Jegeva/BruCON_2021/firmware/main/menu.c

#include "menu.h"
#include "nokialcd.h"
#include "expat.h"
#include "wifi.h"
#if defined(CONFIG_HARDWARE_2020) || defined(CONFIG_HARDWARE_2019)
#include "touch.h"
#include "math.h"
#include "leds.h"
#include <soc/soc.h>
#include <esp_system.h>
#include "battery.h"
#include "sensor.h"
#include "brucon_nvs.h"
#include "mqtt.h"
#endif

uint8_t    menu_dirty    = 1;
uint8_t    currselected  = 0;
menuItem * currMenuItem = NULL ;
char     * statusbartext =NULL;
int        statusbartextallocedssz = 0;

menuItp menuhead;
menuItp schedhead_d1;
menuItp schedhead_d2;
menuItp schedhead_d3;





menuItem fakeplaceholder;
volatile char notaskbar = 0;

void display_skeleton();
void display_taskbar();

void setnotaskbar(int i){
  notaskbar=i;
}

void fixparent(menuItp p, menuItp h)
{
    while(h != NULL){
        h->parent = p;
        h=h->next;
    }
}

char skeleton_inited = 0;

void sched03(void* arg){
    currMenuItem->child = schedhead_d1;
    fixparent(currMenuItem,currMenuItem->child);
    currMenuItem->funcp = NULL;
    manage_click_menu(PIN_BR,0);
};

void sched04(void* arg){
    currMenuItem->child = schedhead_d2;
    fixparent(currMenuItem,currMenuItem->child);
    currMenuItem->funcp = NULL;
    manage_click_menu(PIN_BR,0);

};

void sched05(void* arg){
    currMenuItem->child = schedhead_d3;
    fixparent(currMenuItem,currMenuItem->child);
    currMenuItem->funcp = NULL;
    manage_click_menu(PIN_BR,0);
};



void MapWest(void* arg){
    fakeplaceholder.parent = currMenuItem;
    currMenuItem = &fakeplaceholder;
    MapWestL(arg);
    lcd_sync();
    skeleton_inited = 0;
}

void MapNovo(void* arg){
    fakeplaceholder.parent = currMenuItem;
    currMenuItem = &fakeplaceholder;
    MapNovoL(arg);
    lcd_sync();
    skeleton_inited = 0;
}

void VivaLaVodka(void * arg)
{
  notaskbar=1;
  // for you richard...
  fakeplaceholder.parent = currMenuItem;
  currMenuItem = &fakeplaceholder;
  /*uint32_t score = */
  VivaLaVodkaL(NULL);
  skeleton_inited = 0;
 
}
void VivaLaToothpaste(void * arg)
{
  notaskbar=1;
  // for you richard...
  fakeplaceholder.parent = currMenuItem;
  currMenuItem = &fakeplaceholder;
  /*uint32_t score = */
  VivaLaVodkaL((void*)1);
  skeleton_inited = 0;

}
uint32_t VivaLaToothpasteDirect(void * arg)
{
  // for you richard...
  fakeplaceholder.parent = currMenuItem;
  currMenuItem = &fakeplaceholder;
  /*uint32_t score = */
  uint32_t r=VivaLaVodkaL((void*)1);
  skeleton_inited = 0;
  return r;
}
void SystemInfoL(void* arg)
{
    char * wrkstr = calloc(128,sizeof(char));
    esp_chip_info_t chip_info;
    uint8_t mac[6] ;
    esp_efuse_mac_get_default(mac);
    esp_chip_info(&chip_info);
    memset(wrkstr,0,128);
    lcd_clearB12(B12_WHITE);
    sprintf(wrkstr,"mac %x:%x:%x:%x:%x:%x",
            mac[0],mac[1],mac[2],mac[3],mac[4],mac[5]);

    lcd_setStr(wrkstr,16,2,B12_BLACK,B12_WHITE,0,0);
    sprintf(wrkstr,"%d cores, WiFi%s%s",
            chip_info.cores,
            (chip_info.features & CHIP_FEATURE_BT) ? "/BT" : "",
            (chip_info.features & CHIP_FEATURE_BLE) ? "/BLE" : "");
    lcd_setStr(wrkstr,26,2,B12_BLACK,B12_WHITE,0,0);
    sprintf(wrkstr,"Freq:%dMHz", APB_CLK_FREQ/(1000*1000));
    lcd_setStr(wrkstr,36,2,B12_BLACK,B12_WHITE,0,0);
    sprintf(wrkstr,"bat %d mV %d%%", batteryinfo.vbat,batteryinfo.percent);
    lcd_setStr(wrkstr,46,2,B12_BLACK,B12_WHITE,0,0);
    sprintf(wrkstr,"WiFi ssid: %s", WIFI_SSID);
    lcd_setStr(wrkstr,56,2,B12_BLACK,B12_WHITE,0,0);
    sprintf(wrkstr,"WiFi pw: %s", WIFI_PASSWORD);
    lcd_setStr(wrkstr,66,2,B12_BLACK,B12_WHITE,0,0);

    free(wrkstr);
    display_taskbar();

}



void SystemInfo(void* arg)
{
    fakeplaceholder.parent = currMenuItem;
    currMenuItem = &fakeplaceholder;
    SystemInfoL(NULL);
    lcd_sync();
    skeleton_inited = 0;
}

void EraseKeys(void* arg){
  if( getBruCONConfigFlag("haveKeys") ){
    printf("Erasing keys!\n");
    BruCONErase_key("haveKeys");
    BruCONErase_key("haveClientCert");
    BruCONErase_key("ClientCert");
    BruCONErase_key("POWER_HISTORY");
    BruCONErase_key("UNIQUE_ID");
    BruCONErase_key("EVERSION");
    BruCONErase_key("haveAlcCal");
    printf("Erased keys!\n");
  }
  
}

void RebootF(void* arg){
  printf("REBOOT!\n");
  esp_restart();
}

void testMQTT(void* arg)
{
  printf("TEST MQTT !\n");
  MQTT_Start();
}

void testF(void* arg)
{
  printf("TEST !\n");
  nextwheel(25); 
}
void testF1(void* arg)
{
  printf("TEST 1!\n");
  nextwheelpow(25);
}
void testF2(void* arg)
{
  printf("TEST 2!\n");
  //taskColorWheel();
  taskColorAdvertise();
}

void dispSchedItem(void* arg){
    lcd_clearB12(B12_WHITE);
    char * wrkstr = calloc(128,sizeof(char));
    notaskbar=1;

    memset(wrkstr,0,128);
    sprintf(wrkstr,"Loc: %s",currMenuItem->schedloc);
    lcd_setStr(wrkstr,2,0,B12_BLACK,B12_WHITE,0,1);

    switch(currMenuItem->schedtype){
    case 'W':
        sprintf(wrkstr,"Type: Workshop");
        break;
    case 'T':
        sprintf(wrkstr,"Type: Talk");
        break;

    case 'L':
        sprintf(wrkstr,"Type: General");
        break;

    case 'V':
        sprintf(wrkstr,"Type: Village");

        break;

    case 'S':
        sprintf(wrkstr,"Type: Sp3ci4l");
        break;
    default:
        printf("unknown type %c\n",currMenuItem->schedtype);
    }

    lcd_setStr(wrkstr,32,0,B12_BLACK,B12_WHITE,0,1);
    lcd_setRect(30,0, 30,131, 1, 0);
    lcd_setRect(47,0, 94,131, 1, B12_RED);
    lcd_setStr(currMenuItem->menuText+12,48,0,B12_WHITE,B12_RED,0,1);
    lcd_setRect(46,0, 46,131, 1, 0);
    if(currMenuItem->schedspk != NULL)
        lcd_setStr(currMenuItem->schedspk,96,0,B12_BLACK,B12_WHITE,0,1);
    lcd_setRect(94,0, 94,131, 1, 0);
    free(wrkstr);
    fakeplaceholder.parent = currMenuItem;
    currMenuItem = &fakeplaceholder;

    lcd_sync();
}


#define AUTHORIZED_FUNC_NBR 12

void * menuAuthorisedFunc[AUTHORIZED_FUNC_NBR] = {
    sched03,
    sched04,
    MapWest,
    MapNovo,
    SystemInfo,
    testF,
    testF1,
    testF2,
    RebootF,
    EraseKeys,
    VivaLaVodka,
    VivaLaToothpaste
};

const char * menuAuthorisedFuncName[AUTHORIZED_FUNC_NBR] = {
    "sched03",
    "sched04",
    "MapWest",
    "MapNovo",
    "SystemInfo",
    "testF",
    "testF1",
    "testF2",
    "Reboot",
    "EraseKeys",
    "VivaLaVodka",
    "VivaLaToothpaste"
};

void (*volatile menu_mgt_func)(uint32_t,uint32_t);

void manage_click_menu(uint32_t value,uint32_t level ){
  printf("manage click %d %d\n",value, level);
  menu_mgt_func(value,level);
}

void manage_click_menu_orig(uint32_t value,uint32_t level ){

    int oldrank=currselected;
    menuItem * oldmenuitem = currMenuItem;

//r    printf("click : %d\n",value);

    if(currMenuItem == NULL){
        printf("CURR NULL!\n");

        return;

    }
    //  if(value == PIN_NCHARGING){
    //     printf("clkc: ncharg %d \n",level);
    // }
    if(value == 9999)
        level = 0;

    if(level==0){
//        printf("clkc: %d \n",value);
        if(value != PIN_NCHARGING  && value != 9999){

            switchbacklight(1);
            last_click=xTaskGetTickCount();
            start_bat_task();


        }

        switch(value){
        case 9999:
            display_taskbar();

            printf("battery update : %d vbat : %d mV %d%%\n",  batteryinfo.powstat,batteryinfo.vbat,batteryinfo.percent);
            batt_update=0;
            lcd_sync();
            return;
        case PIN_BL:
            if(currMenuItem->parent != NULL){
                notaskbar=0;
                currMenuItem = currMenuItem->parent;
                currselected = currMenuItem->rank;
                menu_dirty    = 1;
            }
            break;
        case PIN_BR:
            if(currMenuItem->funcp != NULL){
                menu_dirty    = 0;
                currMenuItem->funcp(NULL);
            } else {
               if(currMenuItem->child != NULL){
                    currMenuItem = currMenuItem->child;
                    currselected = currMenuItem->rank;
                    menu_dirty    = 1;
                }
            }
            break;
        case PIN_BU:
            if(currMenuItem->prev != NULL){
                currMenuItem = currMenuItem->prev;
                currselected = currMenuItem->rank;
                menu_dirty    = 1;
            }
            break;
        case PIN_BD:
            if(currMenuItem->next != NULL){
                currMenuItem = currMenuItem->next;
                currselected = currMenuItem->rank;
                menu_dirty    = 1;
            }
            break;
        case PIN_BA:
            if(currMenuItem->parent != NULL){
                notaskbar=0;
                currMenuItem = currMenuItem->parent;
                currselected = currMenuItem->rank;
                menu_dirty    = 1;
            }
            break;
        case PIN_BB:

            if(currMenuItem->funcp != NULL){
                menu_dirty    = 0;
                currMenuItem->funcp(NULL);
            } else {

                if(currMenuItem->child != NULL){
                    currMenuItem = currMenuItem->child;
                    currselected = currMenuItem->rank;
                    menu_dirty    = 1;
                }
            }
            break;
        }
    }
    if(menu_dirty){

        if( ( (value ==PIN_BU ) || ( value == PIN_BD)           ) ){

        if((currselected != 0) && (((currselected%7)==0)&& (value == PIN_BD) ) ){
            return;
        }

        if((value ==PIN_BU ) && (oldrank == 7) )
            return;


        lcd_setRect((((oldrank%7)+1)*16)+1,0, (((oldrank%7)+2)*16)-1,131, 1, B12_WHITE);
        lcd_setStr(oldmenuitem->menuText,(((oldrank%7)+1)*16)+2,0,B12_BLACK,B12_WHITE,0,0);
        lcd_setRect((((currselected%7)+1)*16)+1,0, (((currselected%7)+2)*16)-1,131, 1, B12_RED);
        lcd_setStr(currMenuItem->menuText,(((currselected%7)+1)*16)+2,0,B12_WHITE,B12_RED,0,0);
        lcd_setRect(((oldrank%7)+1)*16,0, ((oldrank%7)+1)*16,131, 1, 0);
        lcd_setRect(((currselected%7)+1)*16,0,((currselected%7)+1)*16,131, 1, 0);
        menu_dirty=1;
        lcd_sync();
        } else {
            ;

        }
    }

}
void * menuAuthorisedFuncByName(char * funcname){
    int i;
    for(i=0;i<AUTHORIZED_FUNC_NBR;i++){
        if(strcmp(funcname,menuAuthorisedFuncName[i]) == 0){
            return menuAuthorisedFunc[i];
        }
    }
    return NULL;
}

void parserMenuTree(menuItp acurrmenuItem,const cJSON* subtree, int depth){
    cJSON *elptr = NULL;
    const cJSON *thisel = NULL;
    menuItp currmenuItem=acurrmenuItem;
    cJSON_ArrayForEach(elptr, subtree){

        thisel = cJSON_GetObjectItemCaseSensitive(elptr, "menutitle");
        if (cJSON_IsString(thisel) && (thisel->valuestring != NULL))
            currmenuItem->menuText= thisel->valuestring;

        thisel = cJSON_GetObjectItemCaseSensitive(elptr, "rank");
        if (cJSON_IsNumber(thisel))
            currmenuItem->rank    = thisel->valueint;

        thisel = cJSON_GetObjectItemCaseSensitive(elptr, "function");
        if (cJSON_IsString(thisel) && (thisel->valuestring != NULL)){
            currmenuItem->funcp = menuAuthorisedFuncByName(thisel->valuestring);
            if(currmenuItem->funcp == NULL){
                printf("unauthorised json function: %s\n",thisel->valuestring);
            }
        }
        thisel = cJSON_GetObjectItemCaseSensitive(elptr, "submenus");
        if(cJSON_IsArray(thisel)){
            //      printf("\nrec\n");
            currmenuItem->child = (menuItp)calloc(1,sizeof(menuItem));
            currmenuItem->child->parent = currmenuItem;
            parserMenuTree(currmenuItem->child,thisel , depth+1);
        }
        if(elptr->next != NULL){
            currmenuItem->next = (menuItp)calloc(1,sizeof(menuItem));
            currmenuItem->next->prev = currmenuItem;
            currmenuItem->next->parent = acurrmenuItem->parent;
            currmenuItem = currmenuItem->next;
        }


    }
//    printf("\nD;%d\n",depth);

}




void parserSchedTreeT(menuItp acurrmenuItem,const cJSON* subtree, int depth){
    cJSON *elptr = NULL;
    const cJSON *thisel = NULL;
    int rank = 0;

    menuItp currmenuItem=acurrmenuItem;

    cJSON_ArrayForEach(elptr, subtree){
        thisel = cJSON_GetObjectItemCaseSensitive(elptr, "title");
        if (cJSON_IsString(thisel) && (thisel->valuestring != NULL)){
            currmenuItem->menuText= thisel->valuestring;
        }
        thisel = cJSON_GetObjectItemCaseSensitive(elptr, "evt");
        if (cJSON_IsString(thisel) && (thisel->valuestring != NULL)){
            currmenuItem->schedtype= *thisel->valuestring;
        }
        thisel = cJSON_GetObjectItemCaseSensitive(elptr, "loc");
        if (cJSON_IsString(thisel) && (thisel->valuestring != NULL)){
            currmenuItem->schedloc = thisel->valuestring;
        }
        thisel = cJSON_GetObjectItemCaseSensitive(elptr, "descr");
        if (cJSON_IsString(thisel) && (thisel->valuestring != NULL)){
            currmenuItem->schedentry = thisel->valuestring;
        }
        thisel = cJSON_GetObjectItemCaseSensitive(elptr, "spk");
        if (cJSON_IsString(thisel) && (thisel->valuestring != NULL)){
            currmenuItem->schedspk = thisel->valuestring;
        }
        currmenuItem->rank = rank++;
        currmenuItem->funcp = dispSchedItem;
        if(elptr->next != NULL){
            currmenuItem->next = (menuItp)calloc(1,sizeof(menuItem));
            currmenuItem->next->prev = currmenuItem;
            currmenuItem = currmenuItem->next;
        }

    }

}

void parserSchedTree(const cJSON* tree){
    schedhead_d1 = calloc(1,sizeof(struct menuIt));
    schedhead_d2 = calloc(1,sizeof(struct menuIt));
    //  schedhead_d3 = calloc(1,sizeof(struct menuIt));

    parserSchedTreeT(schedhead_d1,tree->child,0);
    parserSchedTreeT(schedhead_d2,tree->child->next,0);
    //parserSchedTreeT(schedhead_d3,tree->child->next->next,0);

}
void parserMenuJson(const char* jsonstring,uint8_t issched){
    cJSON *menu_json = cJSON_Parse(jsonstring);
    int depth = 0;
    if (menu_json == NULL)
    {
        const char *error_ptr = cJSON_GetErrorPtr();
        if (error_ptr != NULL){
            fprintf(stderr, "Error before: %s\n", error_ptr);
        }
    }
    if(issched){
        parserSchedTree(menu_json);
    } else {
        menuhead = (menuItp)calloc(1,sizeof(menuItem));
        parserMenuTree(menuhead,menu_json,depth);
    }
    //  cJSON_Delete(menu_json);
    //    return menu_json;
}



void set_status_bar_text(char * b){
    int blen = strlen(b);
    if(blen > statusbartextallocedssz){
        statusbartext = realloc(statusbartext,blen+1);
        statusbartextallocedssz = blen+1;
    }
    strncpy(statusbartext,b,blen);
    *(statusbartext+blen+1)=0;
}

char used[7];

void display_taskbar()
{
    if(notaskbar)
        return;

    uint32_t color = B12_GREEN;
    if( (batteryinfo.powstat & POWSTAT_USB) == 0) {
        color = B12_GREEN;
    } else {
        if( ((batteryinfo.powstat & POWSTAT_STAT1)>0) ==  ((batteryinfo.powstat & POWSTAT_STAT2)>0))
            color = B12_RED;
    }



    lcd_setRect(0,0, 16,131, 1, 0);

    lcd_setRect(6,129, 10,131, 1,color );

    lcd_setRect(4,115, 12,128, 1,color );
    lcd_setRect(5,116, 11,127, 1,0 );
    lcd_setRect(5,116, 11,116 + ceil((float)(11 * ((float)batteryinfo.percent / 100.0F))), 1,B12_WHITE );

    if(batteryinfo.powstat & POWSTAT_USB){
        lcd_setRect( 7,100, 9 ,105, 1,B12_WHITE );
        lcd_setRect( 5,104, 11,105, 1,B12_WHITE );
        lcd_setRect( 4,105, 12,108, 1,B12_WHITE );
        lcd_setRect( 6,108, 6 ,111, 1,B12_WHITE );
        lcd_setRect( 10,108, 10 ,111, 1,B12_WHITE );
    }
    if(wifiIsConnected()){
        lcd_setRect(13,10, 15,12, 1, B12_WHITE);

        lcd_setRect(10,8, 11,14, 1, B12_WHITE);
        lcd_setRect(11,7, 12,8, 1, B12_WHITE);
        lcd_setRect(11,14, 12,15, 1, B12_WHITE);

        lcd_setRect(7,7, 8,15, 1, B12_WHITE);
        lcd_setRect(8,6, 9,7,  1, B12_WHITE);
        lcd_setRect(8,15, 9,16,  1, B12_WHITE);

    }

}


void display_skeleton()
{
    int i;

    menuItem * dispmenuitem = currMenuItem;
    if(! skeleton_inited){
        lcd_clearB12(B12_WHITE);
        lcd_setRect((currselected+1)*16,0, (currselected+2)*16,131, 1, B12_RED);
        skeleton_inited = 1;
    }
    lcd_setRect(0,0, 16,131, 1, 0);

#if defined(CONFIG_HARDWARE_2020) || defined(CONFIG_HARDWARE_2019)

    // batt graph skel
    display_taskbar();
    enable_bat_interrupts();



//    lcd_setRect(3,120, 13,128, 1,B12_WHITE );
#endif

    while((dispmenuitem->prev != NULL) && (dispmenuitem->rank %7 ) )
        dispmenuitem=dispmenuitem->prev;
    i=0;
    while( (i < 7) && (dispmenuitem != NULL) ){
        //if(used[i]){

            lcd_setRect(((i+1)*16)+1,0, ((i+2)*16)-1,131, 1, (i== (currselected%7) )?B12_RED:B12_WHITE);
            //}

        used[i]=1;
        lcd_setStr(dispmenuitem->menuText,((i+1)*16)+2,0,(i==(currselected%7))?B12_WHITE:B12_BLACK,(i==(currselected%7))?B12_RED:B12_WHITE,0,0);
        i++;
        dispmenuitem=dispmenuitem->next;
    }
    while(( i < 7) && used[i])
    {
        used[i]=0;
        lcd_setRect(((i+1)*16)+1,0, ((i+2)*16)-1,131, 1, B12_WHITE);
        i++;
    }

    for(i=1;i<8;i++)
        lcd_setRect(i*16,0, i*16,131, 1, 0);

    lcd_sync();
}

gpio_num_t pins_buttons[7] = { 
    PIN_BL,
    PIN_BR,
    PIN_BU,
    PIN_BD,
    PIN_BA,
    PIN_BB,
    PIN_NCHARGING
};

char pins_levels[7] ;
TickType_t pins_debounce[7];
TickType_t last_click;

#ifdef CONFIG_HARDWARE_2018
 xQueueHandle gpio_evt_queue ;

static void gpio_task_example(void* arg)
{
    uint32_t io_num;
    int pinrank;
    char level;
    char lastlevel;
    // switchbacklight(1);
    for(;;) {
        if(xQueueReceive(gpio_evt_queue, &io_num, portMAX_DELAY)) {
            level = gpio_get_level(io_num);
            printf("gpio evt : %d",io_num);

            switch(io_num){
            case PIN_BL:
                pinrank=0;
                break;
            case PIN_BR:
                pinrank=1;
                break;
            case PIN_BU:
                pinrank=2;
                break;
            case PIN_BD:
                pinrank=3;
                break;
            case PIN_BA:
                pinrank=4;
                break;
            case PIN_BB:
                pinrank=5;
                break;
            case PIN_NCHARGING:
                pinrank=6;
                break;

            default:
                return;
                break;
            }
            lastlevel = pins_levels[pinrank];
            pins_levels[pinrank] = level;
            if( (xTaskGetTickCount()-pins_debounce[pinrank]) > 0){
                pins_debounce[pinrank]=xTaskGetTickCount();
            } else {
                lastlevel=0;
            }


            if( (lastlevel) && (level==0))
                manage_click(io_num,level);
        }


    }
}

static void IRAM_ATTR handler_gpio_buttons(void *args) {
  
    uint32_t gpio_num = (uint32_t) args;


    xQueueSendFromISR(gpio_evt_queue, &gpio_num, NULL);
}
#endif
#if defined(CONFIG_HARDWARE_2020) || defined(CONFIG_HARDWARE_2019)
extern xQueueHandle gpio_evt_queue ;
char enable_input = 0;

static void gpio_task_example(void* arg)
{
    uint32_t io_num;
    int pinrank=0;
    for(;;) {
        if(xQueueReceive(gpio_evt_queue, &io_num, portMAX_DELAY)) {
            //           printf("gpio evt : %d",io_num);
            switch(io_num){
            case PIN_BL:
                pinrank=0;
                break;
            case PIN_BR:
                pinrank=1;
                break;
            case PIN_BU:
                pinrank=2;
                break;
            case PIN_BD:
                pinrank=3;
                break;
            case PIN_BA:
                pinrank=4;
                break;
            case PIN_BB:
                pinrank=5;
                break;
            case 9999:
                pinrank=6;

                break;
            }
            if( (xTaskGetTickCount()-pins_debounce[pinrank]) > 10){
                pins_debounce[pinrank]=xTaskGetTickCount();
                manage_click(io_num,0);
            }
            touch_pad_clear_status();
        }
    }
}


#endif
void print_menu(menuItp aitem, int depth){
    menuItp item = aitem;
    int i=depth;
    do {
        for(i=0;i<depth;i++)
            putchar(' ');
        printf("%s\n",item->menuText);
        if(item->schedentry != NULL){
            printf(" :%s\n",item->schedentry);
        }

        if(item->child)
            print_menu(item->child, depth+1);
        item=item->next;
    } while(item);

}

char    menu_inited=0;
extern const char menu_json_start[] asm("_binary_menu_json_start");
extern const char sched_json_start[] asm("_binary_schedule_sched_filtered_json_start");

char * netsched = NULL;


void display_menu(uint8_t clicked_gui_value)
{

    if(! menu_inited){
        menu_inited=1;



// 2018 hardware

#ifdef CONFIG_HARDWARE_2018
#pragma message "CONFIG2018"
        int i;
        gpio_config_t io_conf;
        gpio_evt_queue = xQueueCreate(10, sizeof(uint32_t));

        io_conf.intr_type = GPIO_PIN_INTR_ANYEDGE;
        io_conf.mode = GPIO_MODE_INPUT;
        io_conf.pull_up_en = 0; // all are physically pulled up
        io_conf.pin_bit_mask =
            (1ULL<<PIN_BR )|
            (1ULL<<PIN_BU )|
            (1ULL<<PIN_BD )|
            (1ULL<<PIN_BA )|
            (1ULL<<PIN_BB )|
            (1ULL<<PIN_BL )
            ;//|            (1ULL<<PIN_NCHARGING );
        //start gpio task
        xTaskCreate(gpio_task_example, "gpio_task_example", 2048, NULL, 10, NULL);
        gpio_config(&io_conf);

        gpio_install_isr_service(0);
        gpio_isr_handler_add(PIN_BL	         , handler_gpio_buttons, (void*)PIN_BL  );
        gpio_isr_handler_add(PIN_BR	         , handler_gpio_buttons, (void*)PIN_BR  );
        gpio_isr_handler_add(PIN_BU	         , handler_gpio_buttons, (void*)PIN_BU  );
        gpio_isr_handler_add(PIN_BD	         , handler_gpio_buttons, (void*)PIN_BD  );
        gpio_isr_handler_add(PIN_BB	         , handler_gpio_buttons, (void*)PIN_BB  );
        gpio_isr_handler_add(PIN_BA	         , handler_gpio_buttons, (void*)PIN_BA  );
        //     gpio_isr_handler_add(PIN_NCHARGING	 , handler_gpio_buttons, (void*)PIN_NCHARGING);
        printf("gpio handlers installed\n");
        for(i=0;i<7;i++){
            pins_levels[i]=1;
        }
#endif
// 2019 hardware
#if defined(CONFIG_HARDWARE_2020) || defined(CONFIG_HARDWARE_2019)
#pragma message "CONFIG2019"
        init_touch();
        xTaskCreate(gpio_task_example, "gpio_task_example", 2048, NULL, 10, NULL);
        update_batteryinfo();

#endif
        parserMenuJson(menu_json_start,0);
        //   print_menu(menuhead,0);
        currMenuItem = menuhead;
        currselected = currMenuItem->rank;


        printf("getting sched\n");


        if(netsched != NULL){
            parserMenuJson(netsched,1);
            free(netsched);

        } else {
            printf("fetching sched broke, using embedded schedule\n");
            parserMenuJson(sched_json_start,1);
        }
        switchbacklight(1);
        start_bat_task();

        /*    print_menu(schedhead_d1,0);
              print_menu(schedhead_d2,0);
              print_menu(schedhead_d3,0);*/


    }
  

    if(menu_dirty){
        display_skeleton(); display_taskbar();
        menu_dirty=0;
    }


}
