Jegeva/BruCON_2021/firmware/main/leds.c

#include "leds.h"
#include "driver/ledc.h"
#include "esp_err.h"
#include "esp_system.h"
#define PIN_LR CONFIG_LED_R_PIN
#define PIN_LG CONFIG_LED_G_PIN
#define PIN_LB CONFIG_LED_B_PIN
#include "freertos/FreeRTOS.h"
#include "freertos/task.h"

char inited=0;
uint16_t sin_col[1024]={
0,3,6,9,12,15,18,21,25,28,31,34,37,40,43,47,50,53,56,59,62,65,69,72,75,78,81,84,87,90,94,97,100,103,106,109,112,115,119,122,125,128,131,134,137,140,144,147,150,153,156,159,162,165,168,171,175,178,181,184,187,190,193,196,199,202,205,209,212,215,218,221,224,227,230,233,236,239,242,245,248,251,254,257,260,264,267,270,273,276,279,282,285,288,291,294,297,300,303,306,309,312,315,318,321,324,327,330,333,336,339,342,344,347,350,353,356,359,362,365,368,371,374,377,380,383,386,388,391,394,397,400,403,406,409,412,414,417,420,423,426,429,432,434,437,440,443,446,449,451,454,457,460,463,466,468,471,474,477,479,482,485,488,491,493,496,499,501,504,507,510,512,515,518,521,523,526,529,531,534,537,539,542,545,547,550,553,555,558,561,563,566,568,571,574,576,579,581,584,587,589,592,594,597,599,602,604,607,609,612,615,617,620,622,625,627,629,632,634,637,639,642,644,647,649,652,654,656,659,661,664,666,668,671,673,675,678,680,683,685,687,690,692,694,696,699,701,703,706,708,710,712,715,717,719,721,724,726,728,730,732,735,737,739,741,743,745,748,750,752,754,756,758,760,762,765,767,769,771,773,775,777,779,781,783,785,787,789,791,793,795,797,799,801,803,805,807,809,811,813,814,816,818,820,822,824,826,828,829,831,833,835,837,839,840,842,844,846,847,849,851,853,854,856,858,860,861,863,865,866,868,870,871,873,875,876,878,879,881,883,884,886,887,889,890,892,894,895,897,898,900,901,903,904,906,907,908,910,911,913,914,916,917,918,920,921,922,924,925,927,928,929,930,932,933,934,936,937,938,939,941,942,943,944,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
            .timer_sel  = LEDC_TIMER_0
        },
	{
            .channel    = LEDC_CHANNEL_2,
            .duty       = 0,
            .gpio_num   = PIN_LB,
            .speed_mode = LEDC_HIGH_SPEED_MODE,
            .hpoint     = 0,
            .timer_sel  = LEDC_TIMER_0
        }
       

};

void init_leds(void){
  ESP_ERROR_CHECK(ledc_timer_config(&ledc_timer));
  for (int ch = 0; ch < 3; ch++) {
    ESP_ERROR_CHECK( ledc_channel_config(&ledc_channel[ch]));
  }
  inited = 1;
}


void set_rgb(unsigned short r,unsigned short g,unsigned short b){
  if(inited == 0)
    init_leds();
  ESP_ERROR_CHECK(ledc_set_duty(ledc_channel[0].speed_mode, ledc_channel[0].channel,r));
  ESP_ERROR_CHECK(ledc_update_duty(ledc_channel[0].speed_mode, ledc_channel[0].channel));
  ESP_ERROR_CHECK(ledc_set_duty(ledc_channel[1].speed_mode, ledc_channel[1].channel,g));
  ESP_ERROR_CHECK(ledc_update_duty(ledc_channel[1].speed_mode, ledc_channel[1].channel));
  ESP_ERROR_CHECK(ledc_set_duty(ledc_channel[2].speed_mode, ledc_channel[2].channel,b));
  ESP_ERROR_CHECK(ledc_update_duty(ledc_channel[2].speed_mode, ledc_channel[2].channel));  
}

void set_rgb8(unsigned char r,unsigned char g,unsigned char b){
  printf("r8 %d %d %d %d %d %d !\n",r,g,b, MAP_8_TO_10_BITS(r),MAP_8_TO_10_BITS(g),MAP_8_TO_10_BITS(b));
  set_rgb( MAP_8_TO_10_BITS(r),MAP_8_TO_10_BITS(g),MAP_8_TO_10_BITS(b));
}

void set_rgb32(unsigned int c){
  set_rgb8((c&0xff0000)>>16,(c&0xff00)>>8,c&0xff);  
}  


volatile unsigned int wheelrank=0;
int power = 256;
int power_raise = 1;
int lin_corr_r=924;
int lin_corr_g=1024;
int lin_corr_b=812;
void setwheel(void){
  set_rgb(

	  gamma_table[((sin_col[(wheelrank    )     ]*power)/1024)*lin_corr_r/1024],
	  gamma_table[((sin_col[(wheelrank+321)%1024]*power)/1024)*lin_corr_g/1024],
	  gamma_table[((sin_col[(wheelrank+681)%1024]*power)/1024)*lin_corr_b/1024]
	  
	  );
  

}

void set_wheelrank(unsigned int rank){


  wheelrank=(rank)%1024;
  //printf("Wheel : %d %d\n",wheelrank,portTICK_PERIOD_MS);
  setwheel();
}

void  set_pow(unsigned int pow){
  power = (pow%1024);
  setwheel();
}

void nextwheel(unsigned int inc){
  set_wheelrank(wheelrank+inc);
}


void nextwheelpow(int inc){
  if(power_raise){
    power += inc;
  }else{
    power -= inc;
  }
  if(power > 1024){
    power = 1024-(power-1024);
    power_raise = !power_raise;
  }
  if(power < 0){
    power = -power;
    power_raise = !power_raise;
  }
  
  set_wheelrank(wheelrank);
}

TaskHandle_t TaskLed=NULL;

void taskColorWheelL(){
  set_wheelrank(esp_random());
  nextwheelpow(10);
  while(1){
    nextwheelpow(10);
    nextwheel(5);
    vTaskDelay(500 / portTICK_PERIOD_MS);
  }
}

void taskColorWheel(){
  if( TaskLed==NULL){
    printf("LedShowOn");
    xTaskCreatePinnedToCore( taskColorWheelL , "LedTask" , 8192, NULL , 5| portPRIVILEGE_BIT , &TaskLed ,0);
  }else{
    printf("LedShowOff");
    vTaskDelete(TaskLed);
    TaskLed=NULL;
    set_wheelrank(0);
    set_pow(0);

  }
}


void taskColorAdvertiseL(){
  while(1){
    set_pow(255);
    vTaskDelay(200 / portTICK_PERIOD_MS);
    set_pow(0);
    vTaskDelay(5000 / portTICK_PERIOD_MS);
  }

}


void taskColorAdvertise(){
  if( TaskLed==NULL){
    printf("LedAdvOn");
    xTaskCreatePinnedToCore( taskColorAdvertiseL , "LedTask" , 8192, NULL , 5| portPRIVILEGE_BIT , &TaskLed ,0);
  }else{
    printf("LedAdvOff");
    vTaskDelete(TaskLed);
    TaskLed=NULL;
    set_wheelrank(0);
    set_pow(0);

  }
}

void starttaskColorAdvertise(unsigned int v){
  if(TaskLed != NULL)
    vTaskDelete(TaskLed);
  TaskLed=NULL;
  set_wheelrank(v);
  xTaskCreatePinnedToCore( taskColorAdvertiseL , "LedTask" , 8192, NULL , 5| portPRIVILEGE_BIT , &TaskLed ,0);   
}


void stoptaskColorAdvertise(){
   if(TaskLed != NULL)
    vTaskDelete(TaskLed);
   set_wheelrank(0);
   set_pow(0);
}
