Jegeva/BruCON_2021/firmware/main/mqtt.h

#ifndef __BRUCON_BADGE_MQTT_H
#define __BRUCON_BADGE_MQTT_H
#include "menu.h"
#include "url.h"
#include "wifi.h"
#include "brucon_nvs.h"
#include "mqtt_client.h"
#include "esp_tls.h"
void MQTT_Start();
void MQTT_Stop();
#endif
