Jegeva/BruCON_2021/firmware/main/settings.priv.h

#ifndef __SETTINGS_PRIV
#define __SETTINGS_PRIV

#ifdef WIFI_PASSWORD
#undef WIFI_PASSWORD
#define WIFI_PASSWORD  "BruCON2020"
#endif


#ifdef WIFI_SSID
#undef WIFI_SSID
#define WIFI_SSID      "brucon"
#endif


#endif
