Jegeva/BruCON_2021/firmware/gamma.py

#! /usr/bin/python
## Creates a gamma-corrected lookup table
import math

def gamma(nsteps, gamma):
    gammaedUp = [math.pow(x, gamma) for x in range(nsteps)]
    return [x/max(gammaedUp) for x in gammaedUp]

def rounder(topValue, gammas):
    return [min(topValue, round(x*topValue)) for x in gammas]

if __name__ == "__main__":
    myGamma = 2.3
    steps = 1024
    output = file("gamma.h", "w")
    output.write("/* %d-step brightness table: gamma = %s */ \n\n" % (steps, myGamma))
    output.write("const uint8_t gamma_table[%d] = {\n" % steps)
    for value in rounder(1024, gamma(steps, myGamma)):
        output.write(" %d," % value)
    output.write("};\n")
    output.close()
